istarendil/crawler/cad/Eje.SLDPRT

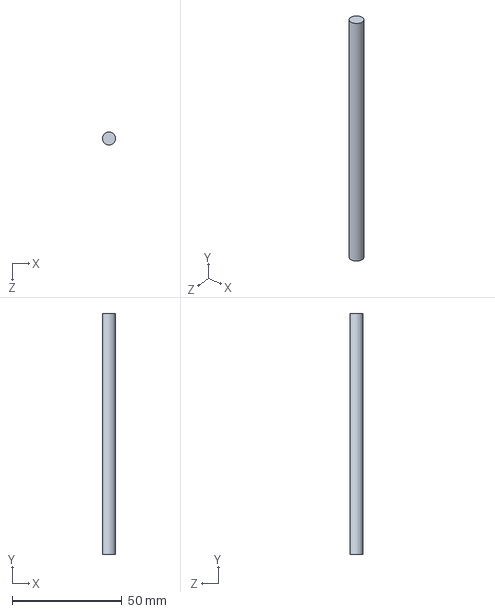
[picture p24: CAD file, 2022-10-31]
cad/Eje.SLDPRT
6.00 x 110.0 x 6.00 mm
