istarendil/crawler/cad/Ajuste-eje.SLDPRT

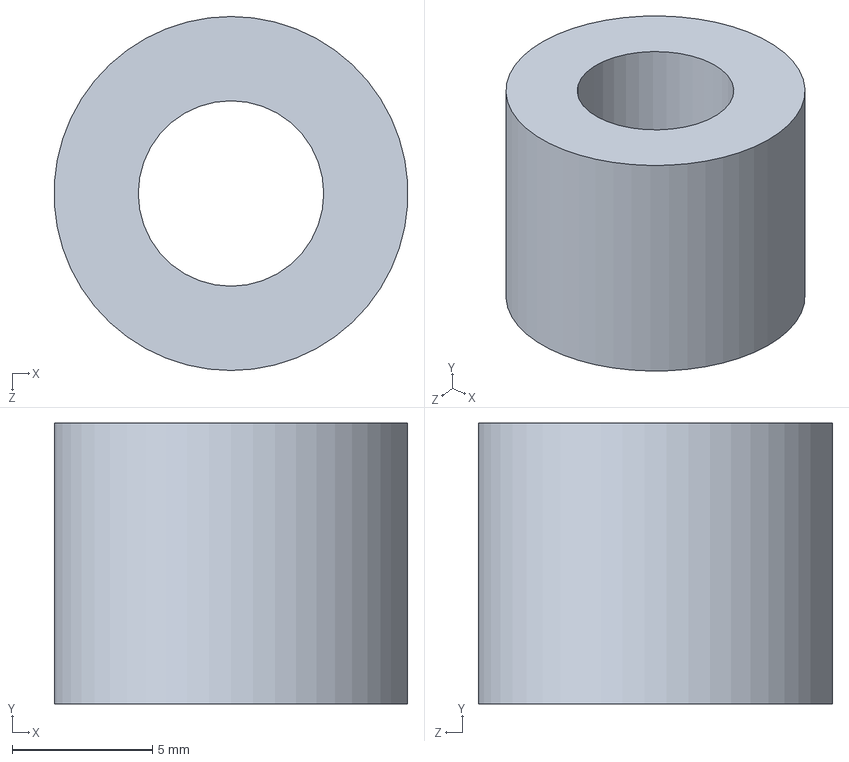
[picture p25: CAD file, 2022-10-31]
cad/Ajuste-eje.SLDPRT
12.6 x 10.0 x 12.6 mm
