istarendil/crawler/cad/Conector_1.SLDPRT

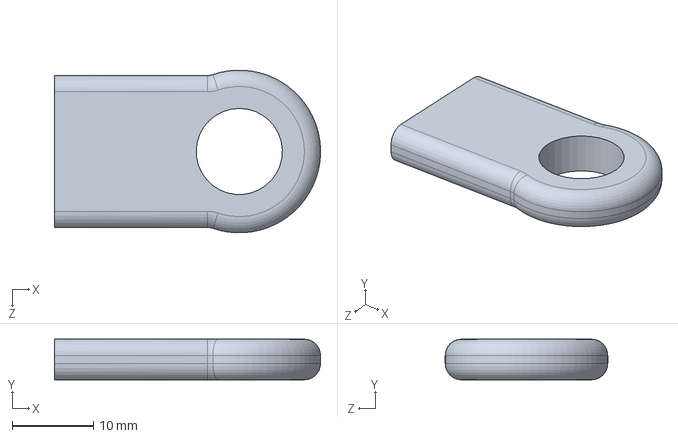
[picture p26: CAD file, 2022-10-31]
cad/Conector_1.SLDPRT
32.7 x 5.00 x 20.0 mm
