istarendil/crawler/cad/Separador3.SLDPRT

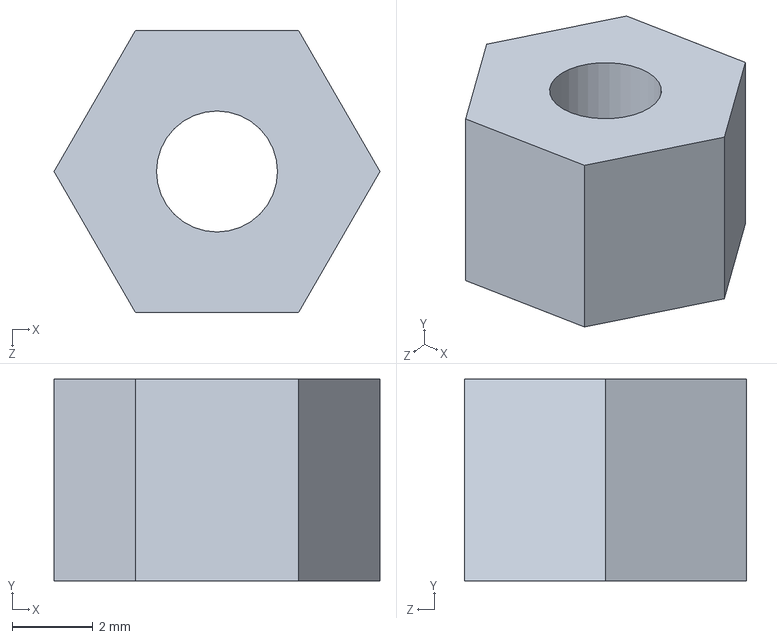
[picture p27: CAD file, 2022-10-31]
cad/Separador3.SLDPRT
8.08 x 5.00 x 7.00 mm
