istarendil/crawler/cad/Chasis2.SLDPRT

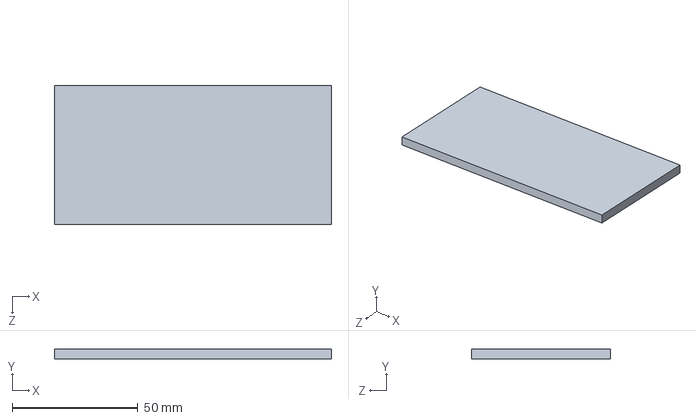
[picture p28: CAD file, 2022-10-31]
cad/Chasis2.SLDPRT
110.0 x 4.00 x 55.0 mm
