istarendil/crawler/cad/Soporte.SLDPRT

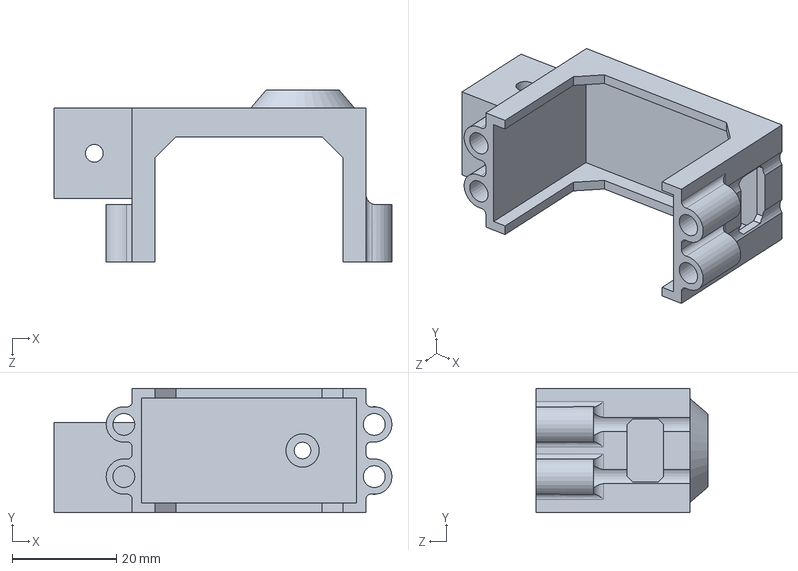
[picture p29: CAD file, 2022-10-31]
cad/Soporte.SLDPRT
64.8 x 23.8 x 33.0 mm
