istarendil/crawler/cad/Separador2.SLDPRT

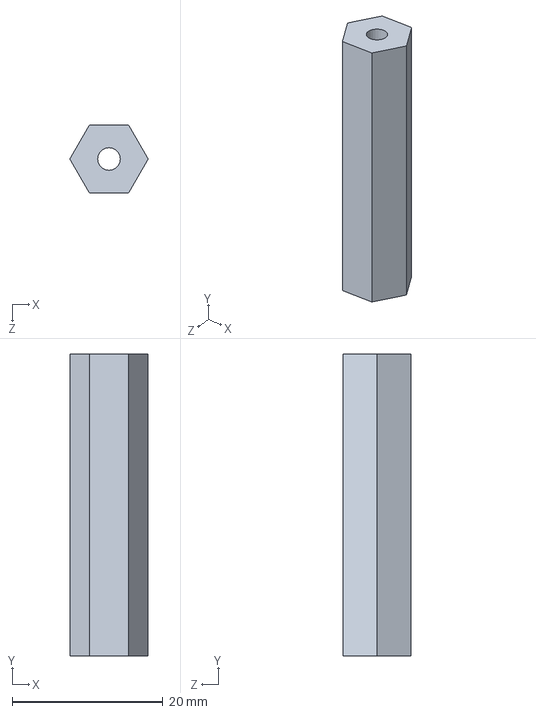
[picture p30: CAD file, 2022-10-31]
cad/Separador2.SLDPRT
10.4 x 40.0 x 9.00 mm
