istarendil/crawler/cad/Pie.SLDPRT

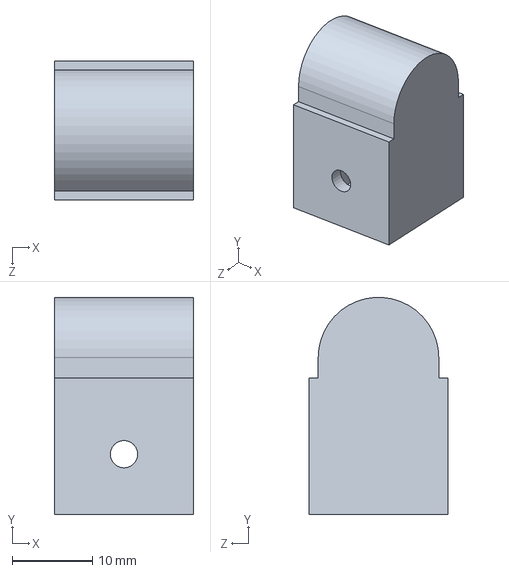
[picture p31: CAD file, 2022-10-31]
cad/Pie.SLDPRT
17.3 x 27.0 x 17.3 mm
