istarendil/crawler/cad/Cople.SLDPRT

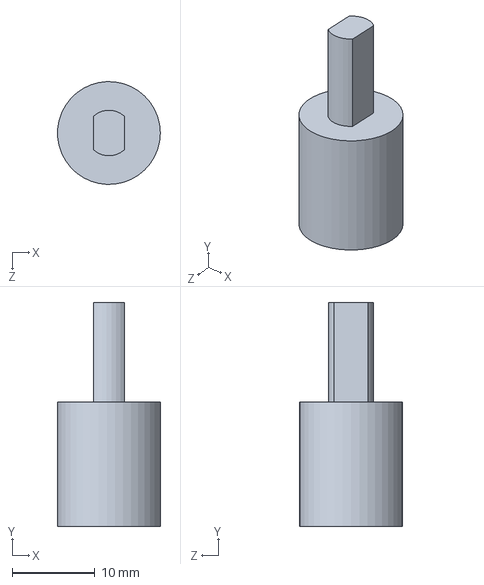
[picture p32: CAD file, 2022-10-31]
cad/Cople.SLDPRT
12.4 x 27.0 x 12.4 mm
